Flygonial/R19-Threaded-Rod-T19-/Drive/R19 Drive Housing.stl

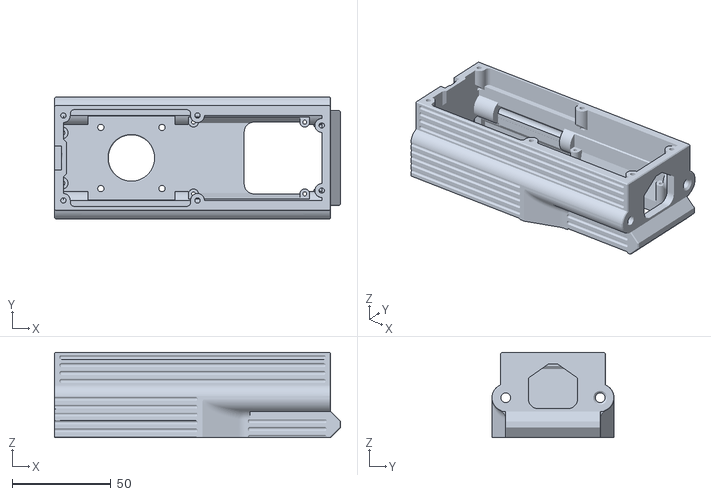
[picture p15: CAD file, 2024-02-16]
Drive/R19 Drive Housing.stl
145.0 x 61.8 x 43.2
