Flygonial/R19-Threaded-Rod-T19-/Grip/R19 Grip Frame.stl

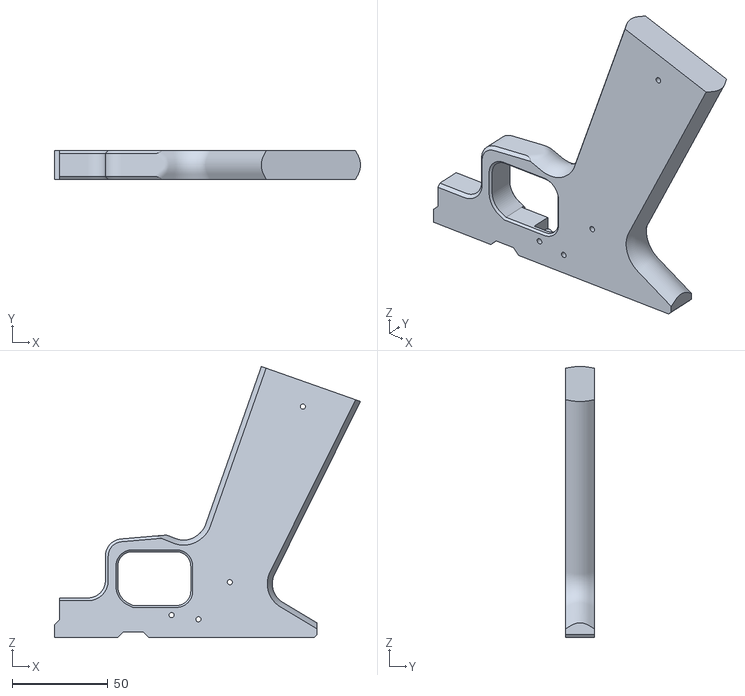
[picture p16: CAD file, 2024-02-16]
Grip/R19 Grip Frame.stl
159.4 x 15.0 x 141.2
