Flygonial/R19-Threaded-Rod-T19-/Magwell/R19 2Way Release.stl

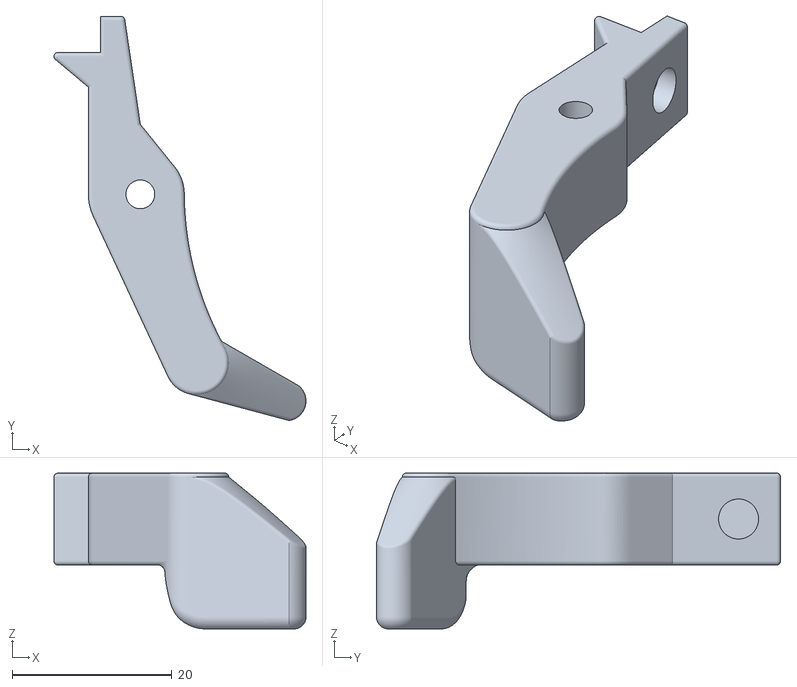
[picture p17: CAD file, 2024-02-16]
Magwell/R19 2Way Release.stl
31.5 x 50.5 x 19.5
