Flygonial/R19-Threaded-Rod-T19-/Stock/R19 Tray Door.stl

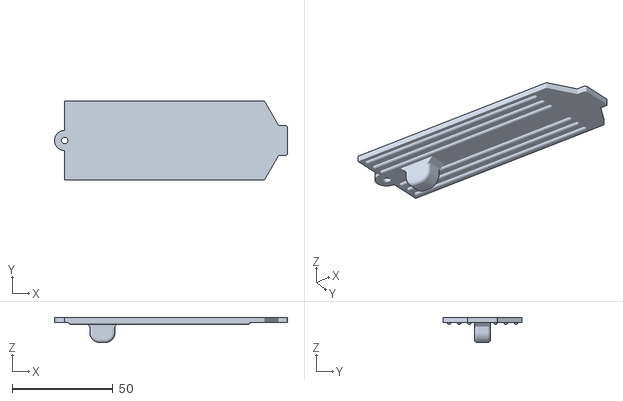
[picture p18: CAD file, 2024-02-16]
Stock/R19 Tray Door.stl
115.5 x 38.9 x 12.5
