Flygonial/R19-Threaded-Rod-T19-/Cage/R19 Delta Cage Rail.stl

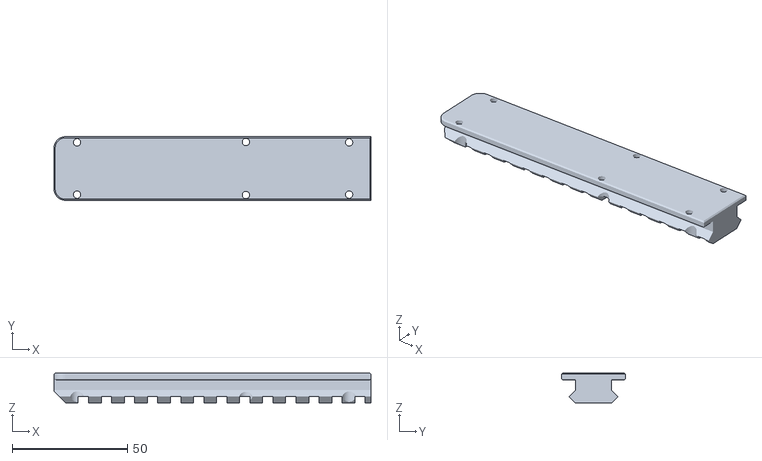
[picture p19: CAD file, 2024-02-16]
Cage/R19 Delta Cage Rail.stl
137.5 x 27.7 x 13.0
