Flygonial/R19-Threaded-Rod-T19-/Drive/R19 Drive Cover.stl

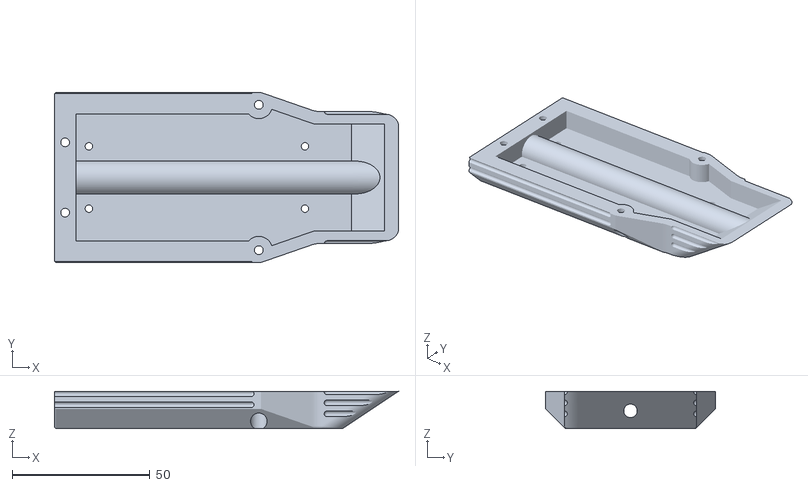
[picture p20: CAD file, 2024-02-16]
Drive/R19 Drive Cover.stl
125.0 x 61.8 x 13.6
