Flygonial/R19-Threaded-Rod-T19-/Grip/R19 Trigger.stl

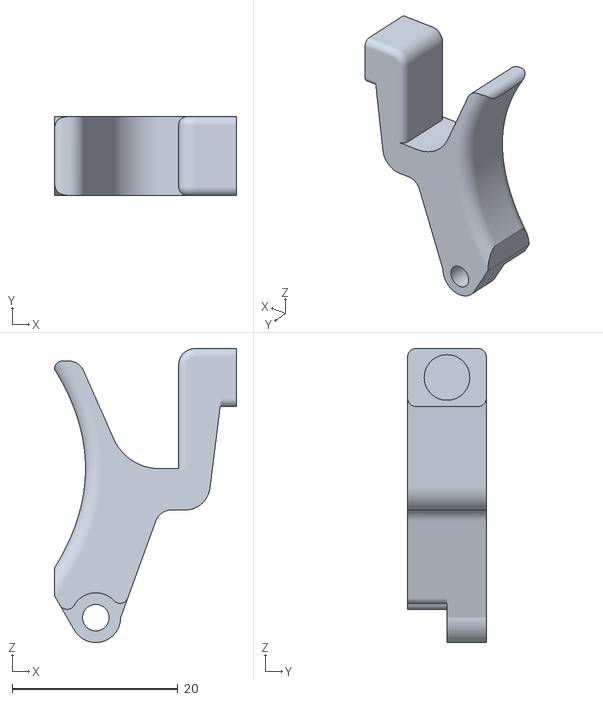
[picture p21: CAD file, 2024-02-16]
Grip/R19 Trigger.stl
22.0 x 9.50 x 35.5
