Flygonial/R19-Threaded-Rod-T19-/Stock/R19 Buttplate.stl

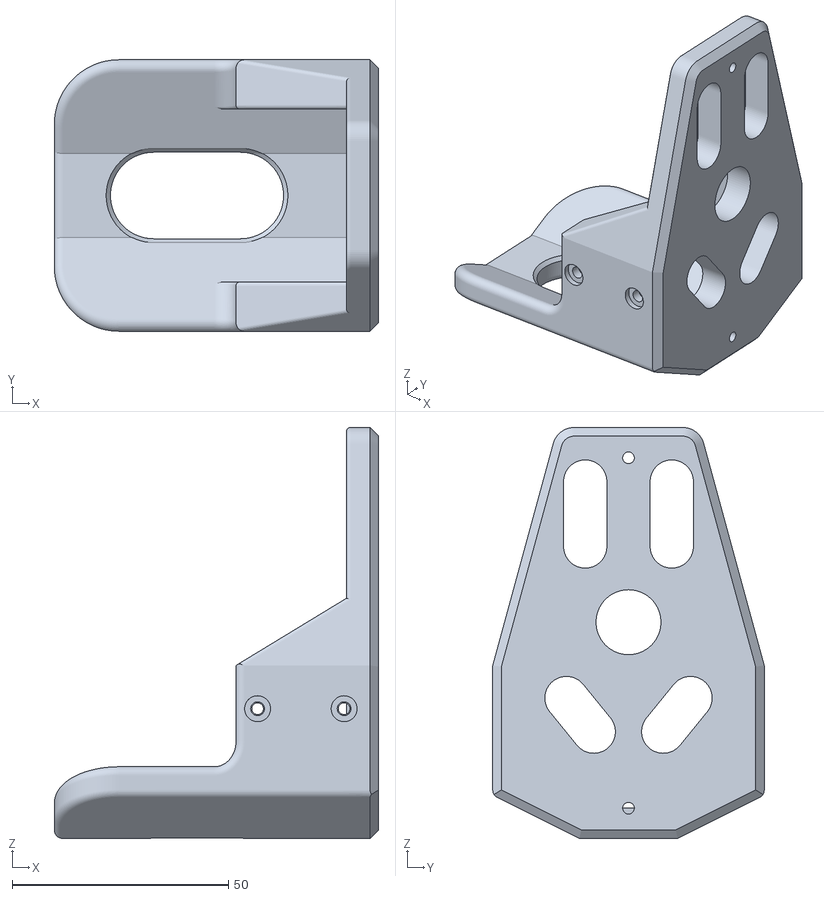
[picture p22: CAD file, 2024-02-16]
Stock/R19 Buttplate.stl
75.0 x 62.8 x 95.0
