Flygonial/R19-Threaded-Rod-T19-/Cage/Hy-Con_Wheels_iFlight_XE_2207_PRO_9.0mm.stl

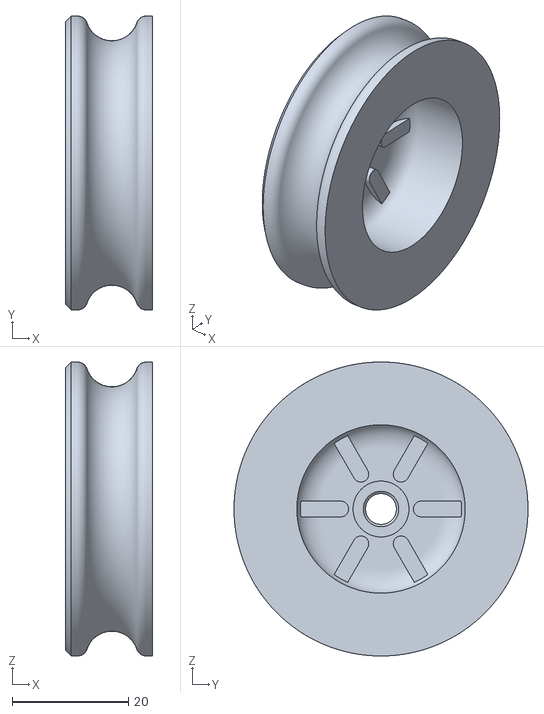
[picture p23: CAD file, 2024-02-16]
Cage/Hy-Con_Wheels_iFlight_XE_2207_PRO_9.0mm.stl
15.0 x 50.5 x 50.5
