Flygonial/R19-Threaded-Rod-T19-/Drive/R19 Drive Spacer.stl

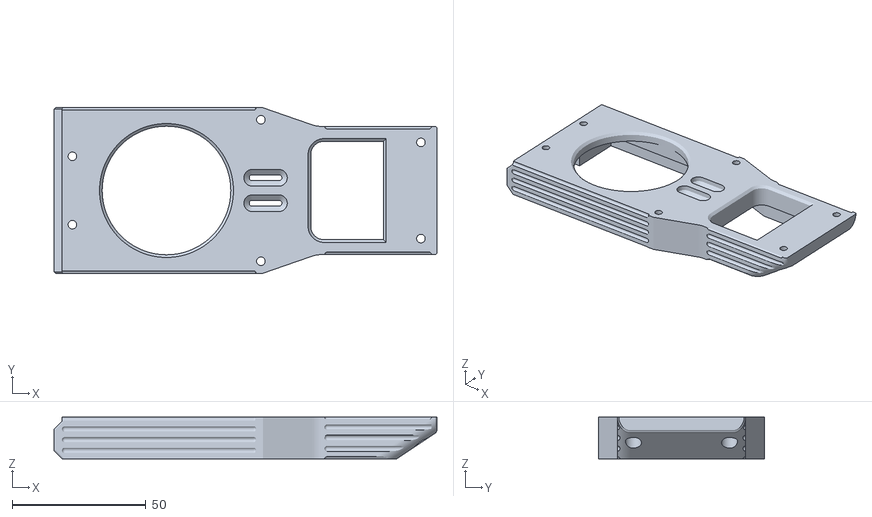
[picture p24: CAD file, 2024-02-16]
Drive/R19 Drive Spacer.stl
143.0 x 61.8 x 15.5
