Flygonial/R19-Threaded-Rod-T19-/Grip/R19 Trigger Cover.stl

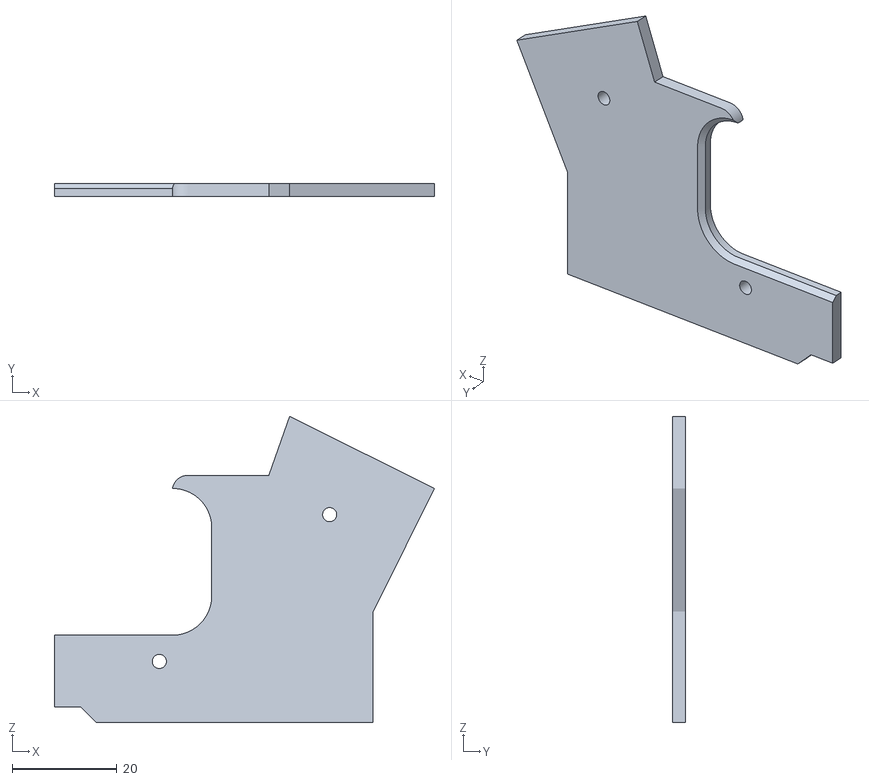
[picture p25: CAD file, 2024-02-16]
Grip/R19 Trigger Cover.stl
72.5 x 2.50 x 58.4
