Flygonial/R19-Threaded-Rod-T19-/Magwell/T19FLRelease.stl

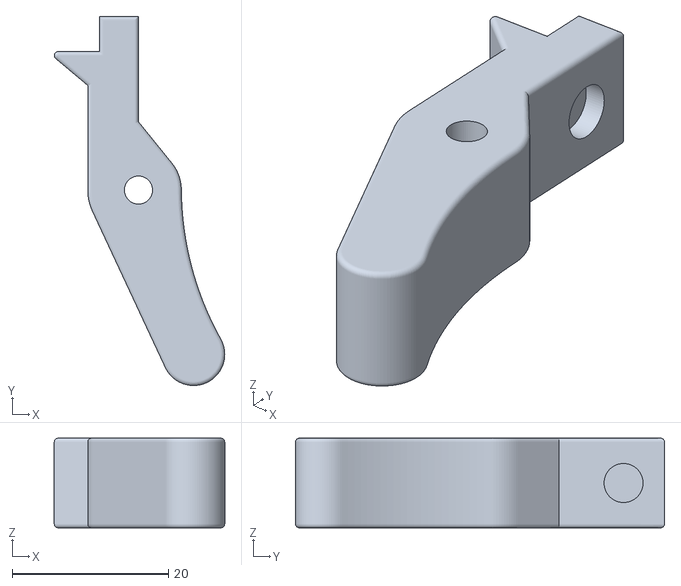
[picture p26: CAD file, 2024-02-16]
Magwell/T19FLRelease.stl
21.9 x 47.3 x 11.5
