Flygonial/R19-Threaded-Rod-T19-/Stock/Flatbar Locking Pin.stl

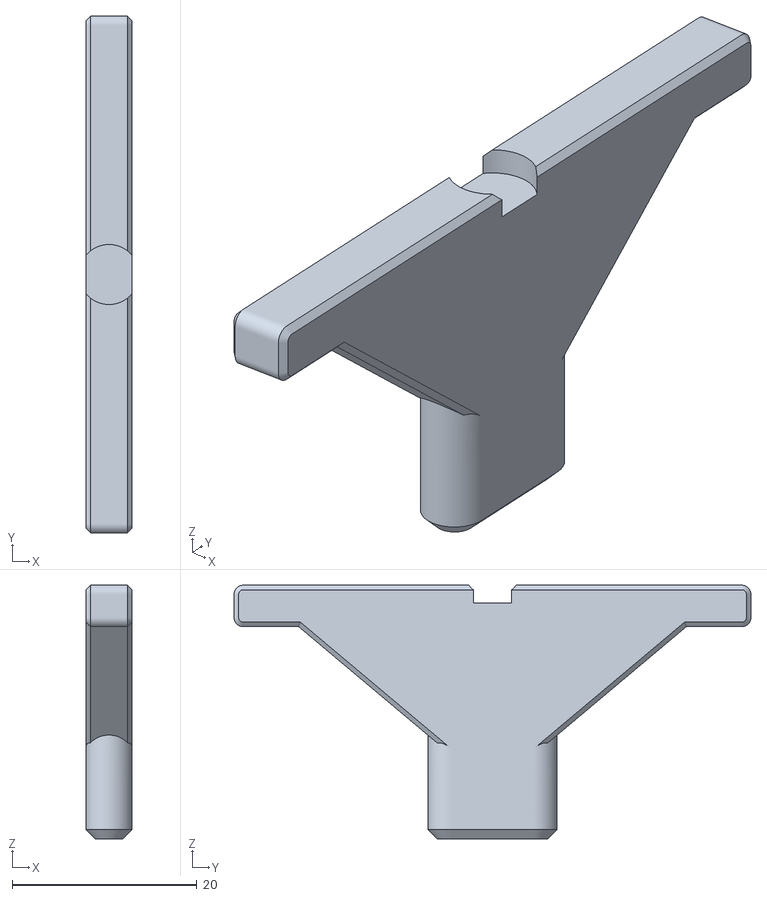
[picture p27: CAD file, 2024-02-16]
Stock/Flatbar Locking Pin.stl
5.00 x 56.0 x 27.5
