Flygonial/R19-Threaded-Rod-T19-/Cage/HyCon Delta BR2207.stl

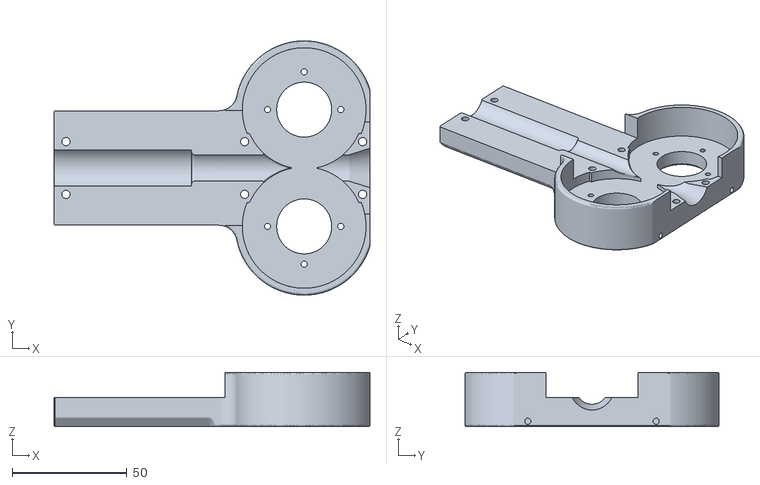
[picture p28: CAD file, 2024-02-16]
Cage/HyCon Delta BR2207.stl
138.0 x 111.1 x 23.8
