Flygonial/R19-Threaded-Rod-T19-/Cage/R19 Underrail.stl

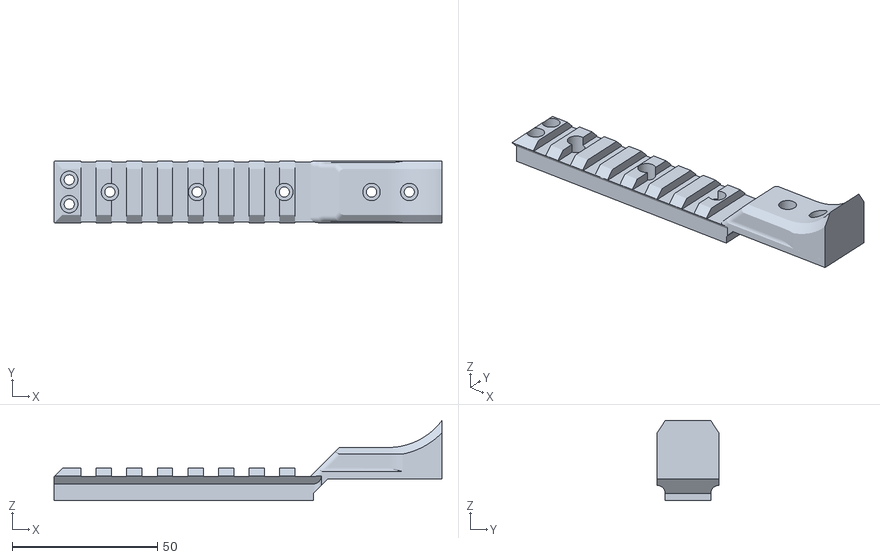
[picture p29: CAD file, 2024-02-16]
Cage/R19 Underrail.stl
133.5 x 21.2 x 27.7
