Flygonial/R19-Threaded-Rod-T19-/Cage/Side Rail Delete.stl

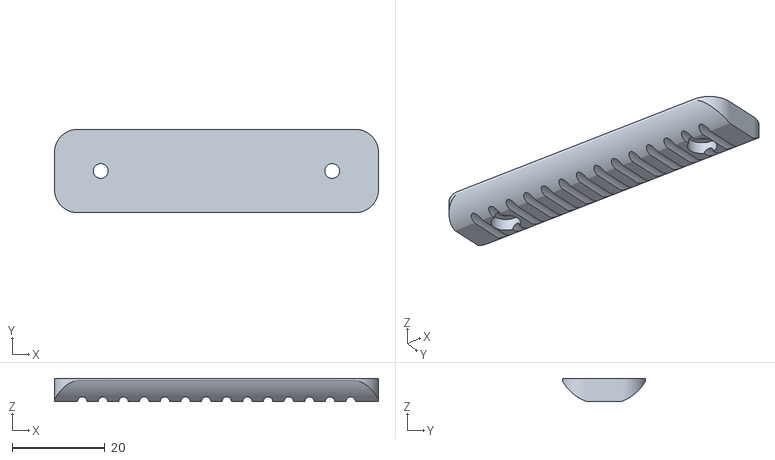
[picture p30: CAD file, 2024-02-16]
Cage/Side Rail Delete.stl
70.0 x 18.0 x 5.00
