Flygonial/R19-Threaded-Rod-T19-/Cage/R19 Cage Adaptor.stl

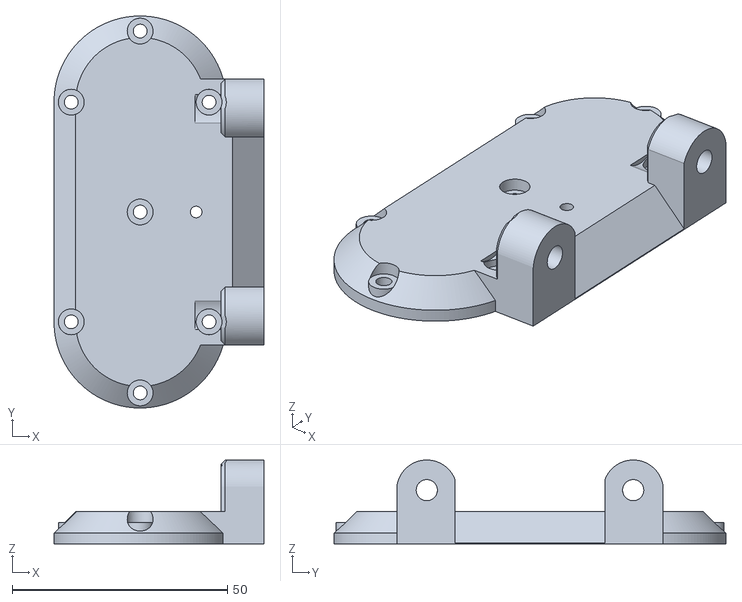
[picture p31: CAD file, 2024-02-16]
Cage/R19 Cage Adaptor.stl
48.8 x 91.0 x 19.5
